arthur2cs/eyzo/firmware/EyzoFirmware/bluetooth_icon.h

#pragma once
#include <Arduino.h>

// Logo Bluetooth affiché sur les écrans d'état connecté/déconnecté/appairage
// (voir drawBluetoothStatus()/drawPairingFrame() dans display_manager.cpp).
// Généré depuis bluetooth.jpg (racine du repo, logo officiel fourni en
// référence) : négatif (fond blanc -> noir, logo noir -> blanc), rogné sur le
// contour du logo puis reposé dans un cadre carré 112x112 (même convention de
// boîte englobante que le logo panda du boot, voir panda_boot_icon.h) — aspect
// ratio d'origine préservé, letterboxé en noir. Valeurs RGB565 natives
// (uint16_t, PAS le format octet big-endian utilisé pour les bitmaps envoyés
// par l'app, voir la note d'endianness en tête de display_manager.cpp) : ce
// tableau est passé tel quel à GFXcanvas16::drawRGBBitmap().
#define BLUETOOTH_ICON_W 112
#define BLUETOOTH_ICON_H 112
static const uint16_t kBluetoothIconRgb565[12544] = {
    0,0,0,0,0,0,0,0,0,0,0,0,
    0,0,0,0,0,0,0,0,0,0,0,0,
    0,0,0,0,0,0,0,0,0,0,0,0,
    0,0,0,0,0,0,0,0,0,0,0,0,
    0,0,0,21162,21162,0,32,0,0,0,0,0,
    0,0,0,0,0,0,0,0,0,0,0,0,
    0,0,0,0,0,0,0,0,0,0,0,0,
    0,0,0,0,0,0,0,0,0,0,0,0,
    0,0,0,0,0,0,0,0,0,0,0,0,
    0,0,0,0,0,0,0,0,0,0,0,0,
    0,0,0,0,0,0,0,0,0,0,0,0,
    0,0,0,0,0,0,0,0,0,0,0,0,
    0,0,0,0,0,0,0,0,0,0,0,0,
    0,0,0,0,0,32,0,23243,65535,14823,0,32,
    0,0,0,0,0,0,0,0,0,0,0,0,
    0,0,0,0,0,0,0,0,0,0,0,0,
    0,0,0,0,0,0,0,0,0,0,0,0,
    0,0,0,0,0,0,0,0,0,0,0,0,
    0,0,0,0,0,0,0,0,0,0,0,0,
    0,0,0,0,0,0,0,0,0,0,0,0,
    0,0,0,0,0,0,0,0,0,0,0,0,
    0,0,0,0,0,0,0,0,0,0,0,0,
    0,0,0,0,0,0,0,0,0,32,0,21162,
    65535,65503,16936,0,32,0,0,0,0,0,0,0,
    0,0,0,0,0,0,0,0,0,0,0,0,
    0,0,0,0,0,0,0,0,0,0,0,0,
    0,0,0,0,0,0,0,0,0,0,0,0,
    0,0,0,0,0,0,0,0,0,0,0,0,
    0,0,0,0,0,0,0,0,0,0,0,0,
    0,0,0,0,0,0,0,0,0,0,0,0,
    0,0,0,0,0,0,0,0,0,0,0,0,
    0,0,0,0,0,0,0,0,0,0,0,0,
    0,32,0,21162,65535,65535,65535,19017,0,32,0,0,
    0,0,0,0,0,0,0,0,0,0,0,0,
    0,0,0,0,0,0,0,0,0,0,0,0,
    0,0,0,0,0,0,0,0,0,0,0,0,
    0,0,0,0,0,0,0,0,0,0,0,0,
    0,0,0,0,0,0,0,0,0,0,0,0,
    0,0,0,0,0,0,0,0,0,0,0,0,
    0,0,0,0,0,0,0,0,0,0,0,0,
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
};
